lukehsiao/CribSense/docs/img/pi-camera-cable.jpg

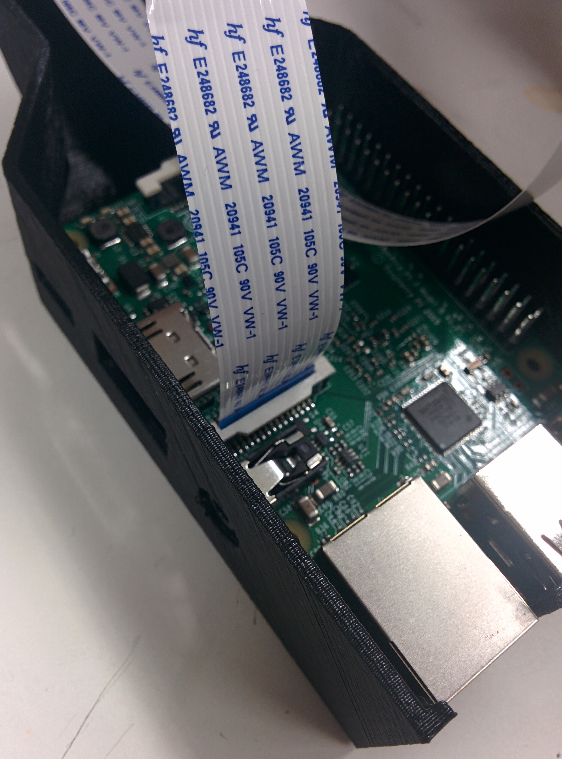
docs/img/pi-camera-cable.jpg
