lukehsiao/CribSense/docs/img/pi-not-glued.jpg

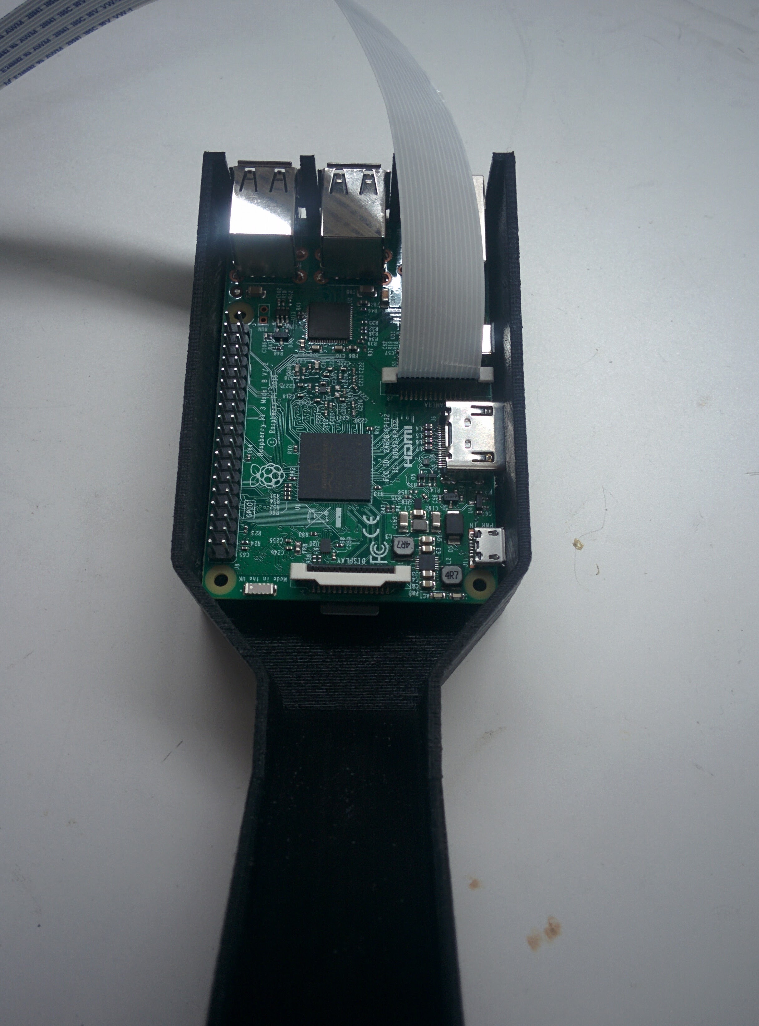
docs/img/pi-not-glued.jpg
